sbv1307/ESP32-energy-meter-MQTT/Hardware/energiRegistrationForHA.kicad_sch

## KiCad design Hardware/energiRegistrationForHA.kicad_sch (2025-07-06)

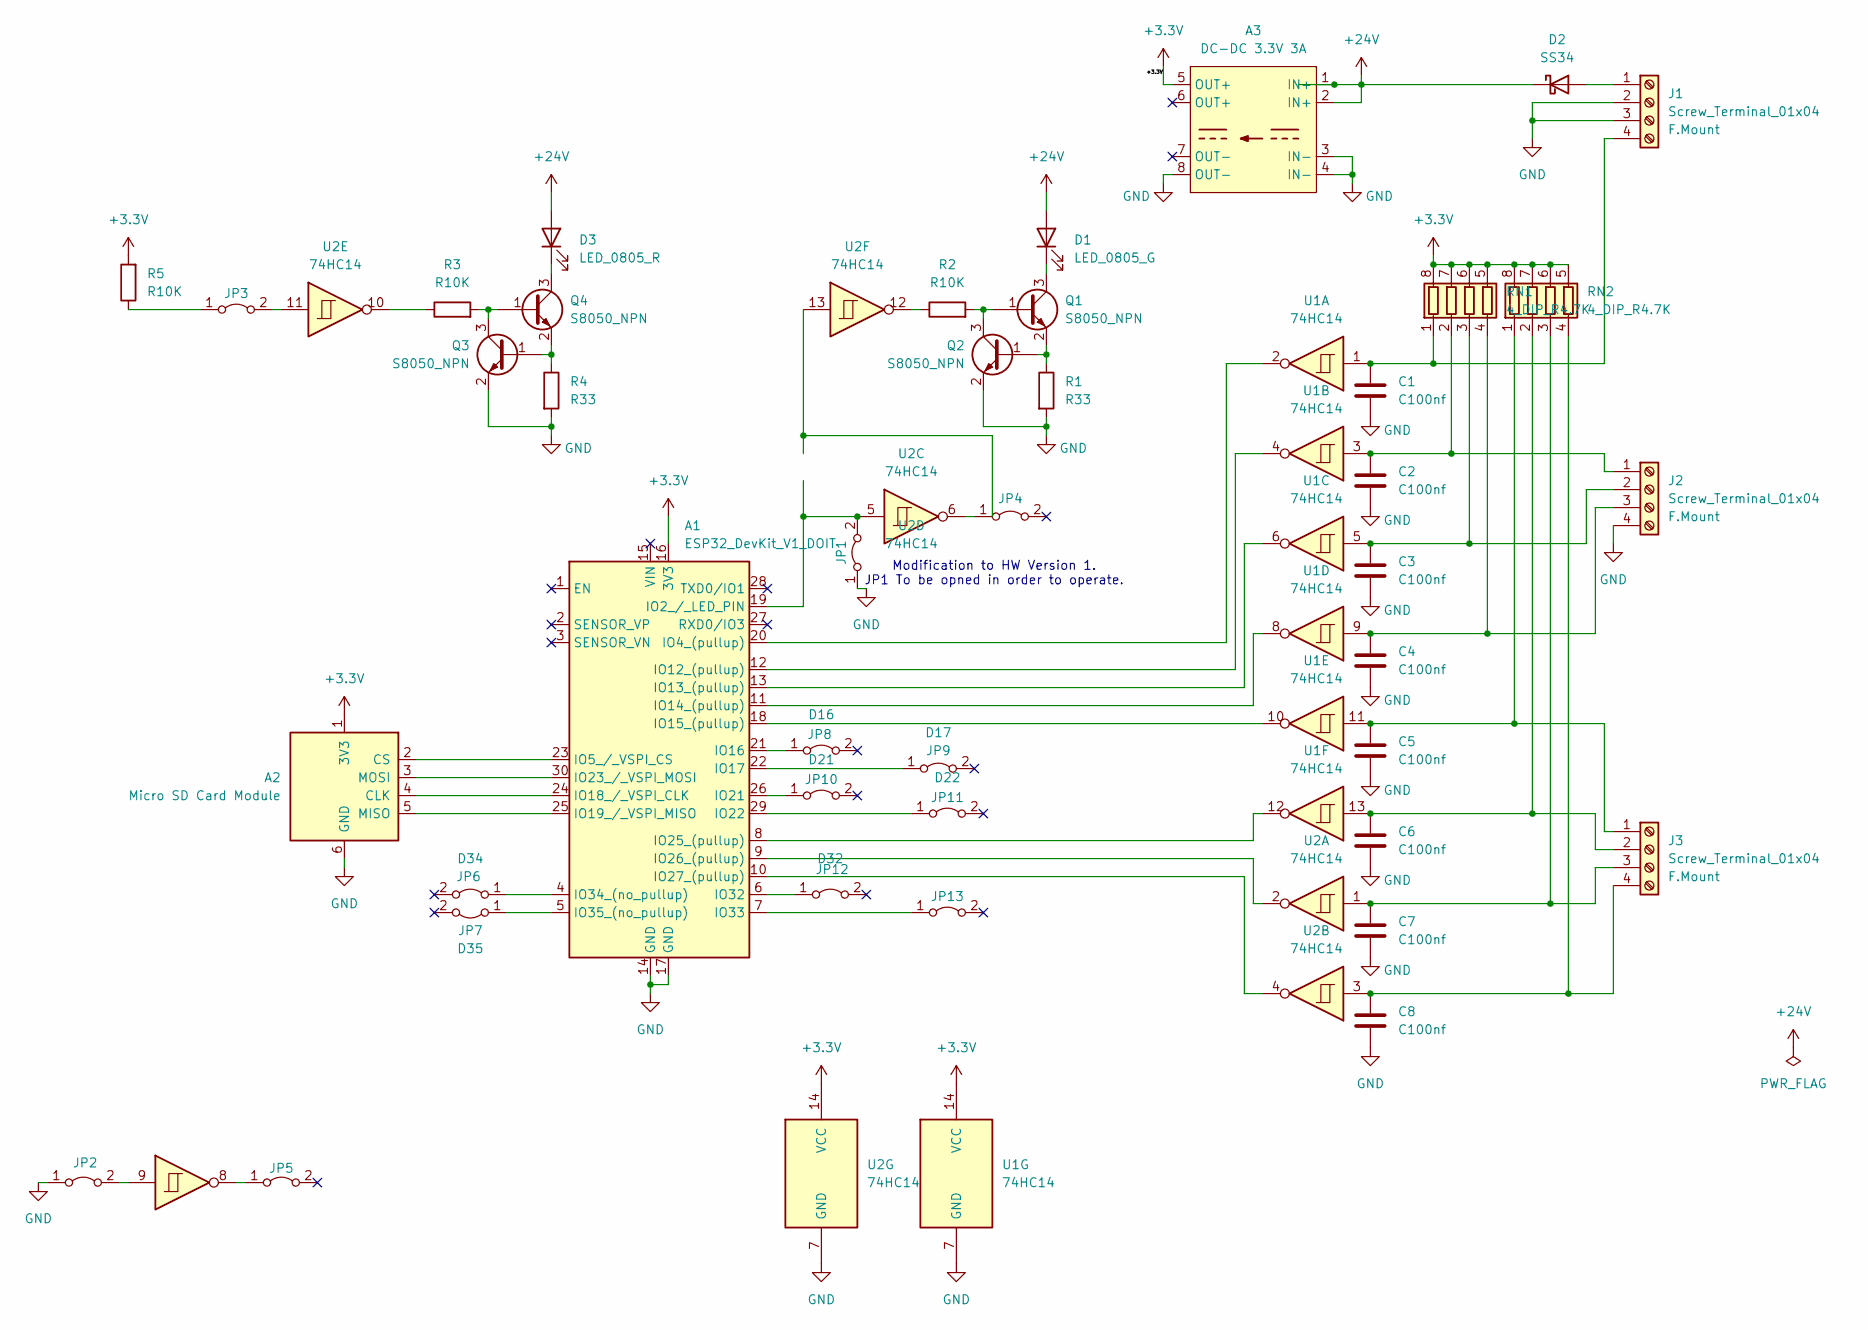
[picture p2: schematic energiRegistrationForHA.kicad_sch]

Parts:
A1: ESP32_DevKit_V1_DOIT; esp32_devkit_v1_doit (F.Mount)
A2: Micro SD Card Module; Micro SD PinHeader_1x06_P2.54mm_Vertical_(F.Mount)
A3: DC-DC 3.3V 3A; DC-DC_3.3V_3A_Stepdown (F.Mount); MFR. Part # N/A; JLCBCB Part N/A
C1, C2, C3, C4, C5, C6, C7, C8: C100nf; C_0402_1005Metric; MFR. Part # CL05B104KO5NNNC; JLCPCB Part # C1525
D1: LED_0805_G; LED_0805_2012Metric; MFR. Part # KT-0805G; JLCPCB Part # C2297
D2: SS34; D_SMA; MFR. Part # SS34; JLCPCB Part # C8678
D3: LED_0805_R; LED_0805_2012Metric; MFR. Part # NCD0805R1; JLCPCB Part # C84256
J1, J2, J3: Screw_Terminal_01x04; TerminalBlock_PT-1,5-4-5.0-H_1x04_P5.00mm_Horizontal-(F.Mou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; MFR. Part # 950-T-DS/02; Digi-Key Part # 3072-950-T-DS/02-ND
JP1, JP2, JP3, JP4, JP5: SolderJumper_2_Bridged; SolderJumper-2_P1.3mm_Bridged_RoundedPad1.0x1.5mm(F.Mount)
JP6: D34; SolderJumper-2_P1.3mm_Bridged_RoundedPad1.0x1.5mm(F.Mount)
JP7: D35; SolderJumper-2_P1.3mm_Bridged_RoundedPad1.0x1.5mm(F.Mount)
JP8: D16; SolderJumper-2_P1.3mm_Bridged_RoundedPad1.0x1.5mm(F.Mount)
JP9: D17; SolderJumper-2_P1.3mm_Bridged_RoundedPad1.0x1.5mm(F.Mount)
JP10: D21; SolderJumper-2_P1.3mm_Bridged_RoundedPad1.0x1.5mm(F.Mount)
JP11: D22; SolderJumper-2_P1.3mm_Bridged_RoundedPad1.0x1.5mm(F.Mount)
JP12: D32; SolderJumper-2_P1.3mm_Bridged_RoundedPad1.0x1.5mm(F.Mount)
JP13: D33; SolderJumper-2_P1.3mm_Bridged_RoundedPad1.0x1.5mm(F.Mount)
Q1, Q2, Q3, Q4: S8050_NPN; SOT-23; MFR. Part # SS8050; JLCPCB Part # C2150
R1, R4: R33; R_0805_2012Metric; MFR. Part # 0805W8F330JT5E; JLCPCB Part # C17634
R2, R3, R5: R10K; R_0402_1005Metric; MFR. Part # 0402WGF1002TCE; JLCPCB Part # C25744
RN1, RN2: 4_DIP_R4.7K; RES-ARRAY-SMD_0603-8P-L3.2-W1.6-BL; MFR. Part # 4D03WGJ0472T5E; JLCPCB Part # C1980
U1, U2: 74HC14; SOIC-14_3.9x8.7mm_P1.27mm; MFR. Part # 74HC14D,653; JLCPCB Part # C5605

Connections:
+3.3V: A1.16 (3V3), A2.1 (3V3), A3.5 (OUT+), R5.2, RN1.5 (R4.2), RN1.6 (R3.2), RN1.7 (R2.2), RN1.8 (R1.2), RN2.5 (R4.2), RN2.6 (R3.2), RN2.7 (R2.2), RN2.8 (R1.2), U1.14 (VCC), U2.14 (VCC)
+24V: A3.1 (IN+), A3.2 (IN+), D1.2 (A), D2.1 (K), D3.2 (A)
GND: A1.14 (GND), A1.17 (GND), A2.6 (GND), A3.3 (IN-), A3.4 (IN-), A3.8 (OUT-), C1.2, C2.2, C3.2, C4.2, C5.2, C6.2, C7.2, C8.2, J1.2, J1.3, J2.4, JP1.1 (A), JP2.1 (A), Q2.2 (E), Q3.2 (E), R1.2, R4.2, U1.7 (GND), U2.7 (GND)
unnamed: A1.4 (IO34_(no_pullup)), JP6.1 (A)
unnamed: A1.5 (IO35_(no_pullup)), JP7.1 (A)
unnamed: A1.6 (IO32), JP12.1 (A)
unnamed: A1.7 (IO33), JP13.1 (A)
unnamed: A1.8 (IO25_(pullup)), U1.12
unnamed: A1.9 (IO26_(pullup)), U2.2
unnamed: A1.10 (IO27_(pullup)), U2.4
unnamed: A1.11 (IO14_(pullup)), U1.8
unnamed: A1.12 (IO12_(pullup)), U1.4
unnamed: A1.13 (IO13_(pullup)), U1.6
unnamed: A1.18 (IO15_(pullup)), U1.10
unnamed: A1.19 (IO2_/_LED_PIN), JP1.2 (B), U2.5
unnamed: A1.20 (IO4_(pullup)), U1.2
unnamed: A1.21 (IO16), JP8.1 (A)
unnamed: A1.22 (IO17), JP9.1 (A)
unnamed: A1.23 (IO5_/_VSPI_CS), A2.2 (CS)
unnamed: A1.24 (IO18_/_VSPI_CLK), A2.4 (CLK)
unnamed: A1.25 (IO19_/_VSPI_MISO), A2.5 (MISO)
unnamed: A1.26 (IO21), JP10.1 (A)
unnamed: A1.29 (IO22), JP11.1 (A)
unnamed: A1.30 (IO23_/_VSPI_MOSI), A2.3 (MOSI)
unnamed: C1.1, J1.4, RN1.1 (R1.1), U1.1
unnamed: C2.1, J2.1, RN1.2 (R2.1), U1.3
unnamed: C3.1, J2.2, RN1.3 (R3.1), U1.5
unnamed: C4.1, J2.3, RN1.4 (R4.1), U1.9
unnamed: C5.1, J3.1, RN2.1 (R1.1), U1.11
unnamed: C6.1, J3.2, RN2.2 (R2.1), U1.13
unnamed: C7.1, J3.3, RN2.3 (R3.1), U2.1
unnamed: C8.1, J3.4, RN2.4 (R4.1), U2.3
unnamed: D1.1 (K), Q1.3 (C)
unnamed: D2.2 (A), J1.1
unnamed: D3.1 (K), Q4.3 (C)
unnamed: JP2.2 (B), U2.9
unnamed: JP3.1 (A), R5.1
unnamed: JP3.2 (B), U2.11
unnamed: JP4.1 (A), U2.6
unnamed: JP5.1 (A), U2.8
unnamed: Q1.1 (B), Q2.3 (C), R2.2
unnamed: Q1.2 (E), Q2.1 (B), R1.1
unnamed: Q3.1 (B), Q4.2 (E), R4.1
unnamed: Q3.3 (C), Q4.1 (B), R3.2
unnamed: R2.1, U2.12
unnamed: R3.1, U2.10

Notes on the sheet:
Modification to HW Version 1. JP1 To be opned in order to operate.
